mattwach/battery_drainer/images/buttons.png

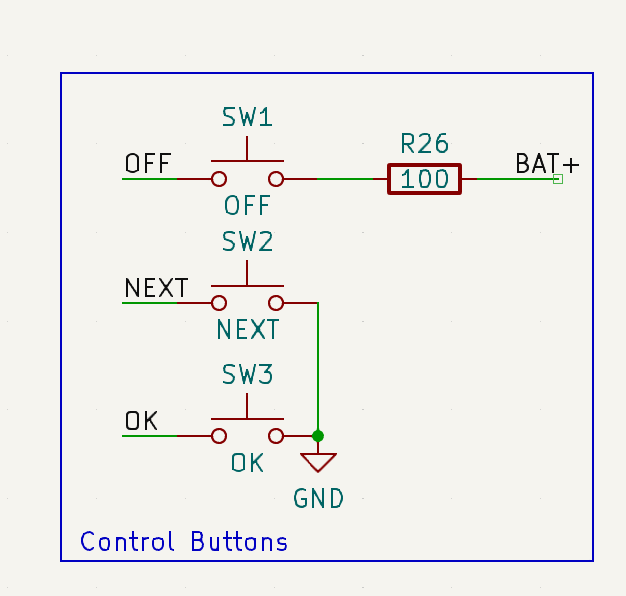
images/buttons.png
