mattwach/battery_drainer/src/test/oled/main.c

#include <oledm/oledm.h>
#include <oledm/text.h>
#include <oledm/font/terminus8x16.h>
#include "pico/stdlib.h"

#define OLEDM_INIT oledm_basic_init

struct OLEDM display;
struct Text text;

static void enable() {
    const uint ENABLE_PIN = 21;
    gpio_init(ENABLE_PIN);
    gpio_set_dir(ENABLE_PIN, GPIO_OUT);
    gpio_put(ENABLE_PIN, 1);
}

int main(void) {
  enable();
  OLEDM_INIT(&display);
  oledm_start(&display);

  oledm_clear(&display, 0x00);

  oledm_set_bounds(&display, 0, 0, display.visible_columns - 1, 0);
  oledm_start_pixels(&display);
  int x = 0;
  for (; x < display.visible_columns; ++x) {
    uint8_t b = 0x00;
    if ((x == 0) || (x >= 127)) {
      b = 0xFF;
    } else if (!(x & 0x07)) {
      if (!(x & 0x0F)) {
        b = 0x0F;
      } else {
        b = 0x03;
      }
    }
    oledm_write_pixels(&display, b);
  }
  oledm_stop(&display);

  text_init(&text, terminus8x16, &display);
  text.row = 2;
  text_str(&text, "Hello World!");
}
